vonkonow/LeetAI/firmware/assets/images/chord0.bmp

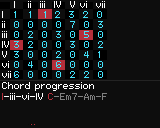
firmware/assets/images/chord0.bmp
